jberman3039/Digital-Analog-Watch/src/ds3231.h

void get_seconds(unsigned char* seconds);
void get_minutes(unsigned char* minutes);
void get_hours(unsigned char* hours);
void set_seconds(unsigned short seconds);
void set_minutes(unsigned short minutes);
void set_hours(unsigned short hours);
